sparkfun/Pi_grammer/Documentation_ example_&_pics/ISOLATE_ADD-ON_control_line.jpg

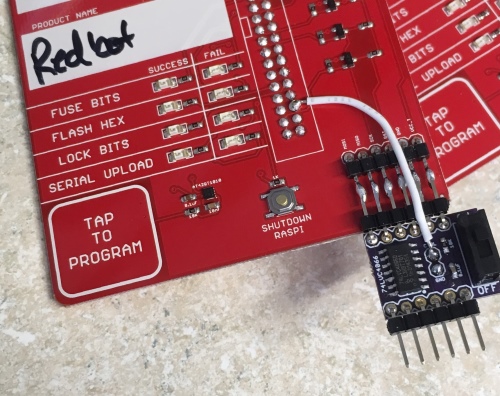
Documentation_ example_&_pics/ISOLATE_ADD-ON_control_line.jpg
