sparkfun/Pi_grammer/Documentation_ example_&_pics/stat.jpg

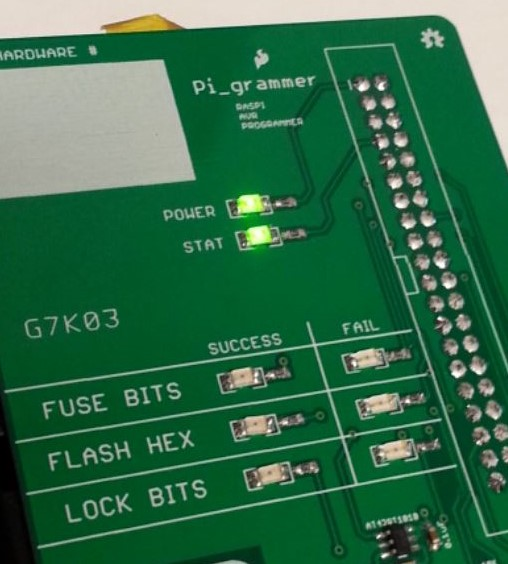
Documentation_ example_&_pics/stat.jpg
