sparkfun/Pi_grammer/Documentation_ example_&_pics/tap.jpg

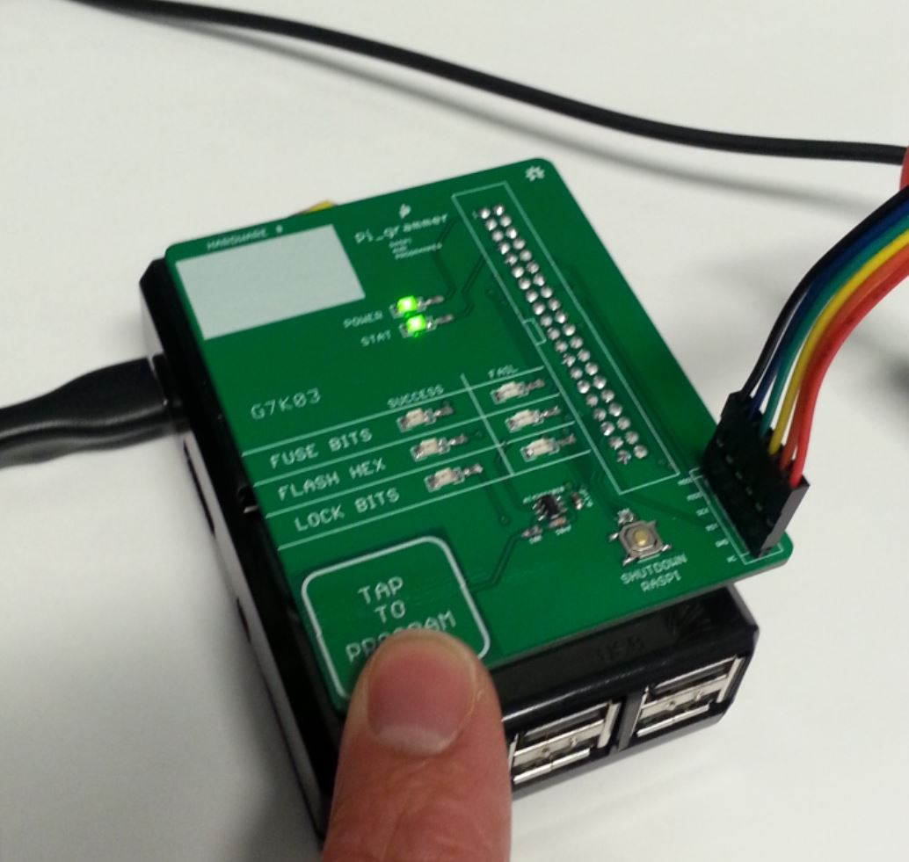
Documentation_ example_&_pics/tap.jpg
