sparkfun/Pi_grammer/Documentation_ example_&_pics/V20_pics/power.jpg

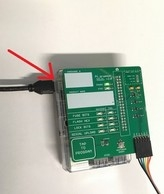
Documentation_ example_&_pics/V20_pics/power.jpg
