sparkfun/Pi_grammer/Documentation_ example_&_pics/V20_pics/success.jpg

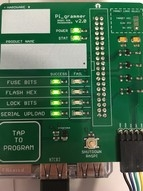
Documentation_ example_&_pics/V20_pics/success.jpg
